manos-space/TAS_kc/keycaps/SLS/sldprt/r0/r0_c3.SLDPRT

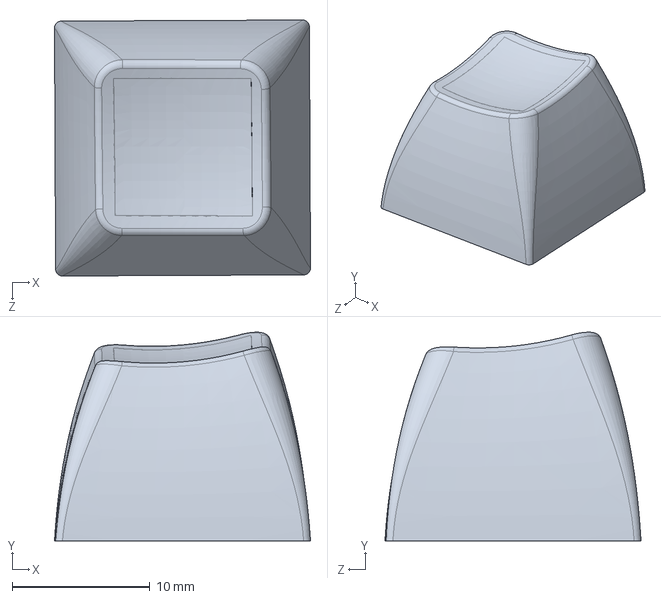
[picture p15: CAD file, 2020-01-13]
keycaps/SLS/sldprt/r0/r0_c3.SLDPRT
18.6 x 15.1 x 18.6 mm
