manos-space/TAS_kc/keycaps/SLS/sldprt/r1/r1_c1.SLDPRT

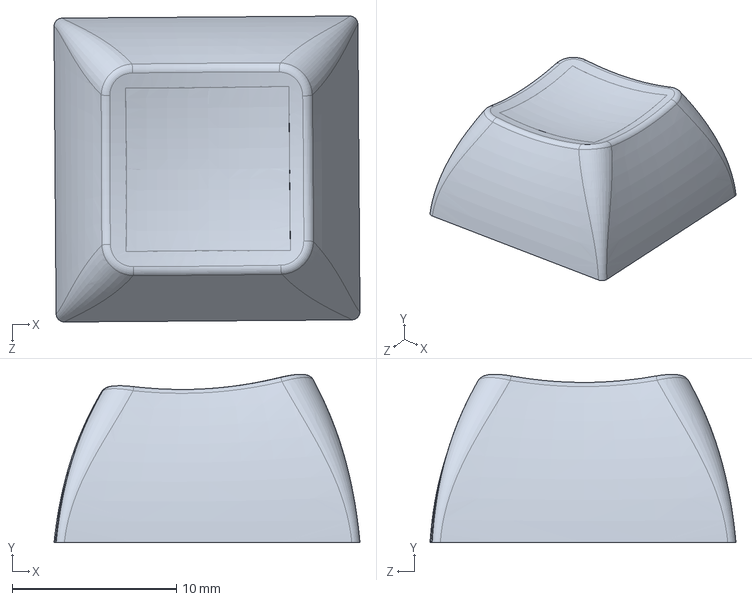
[picture p16: CAD file, 2020-01-13]
keycaps/SLS/sldprt/r1/r1_c1.SLDPRT
18.6 x 10.3 x 18.6 mm
