manos-space/TAS_kc/keycaps/SLS/sldprt/r3/r3-1.25u.SLDPRT

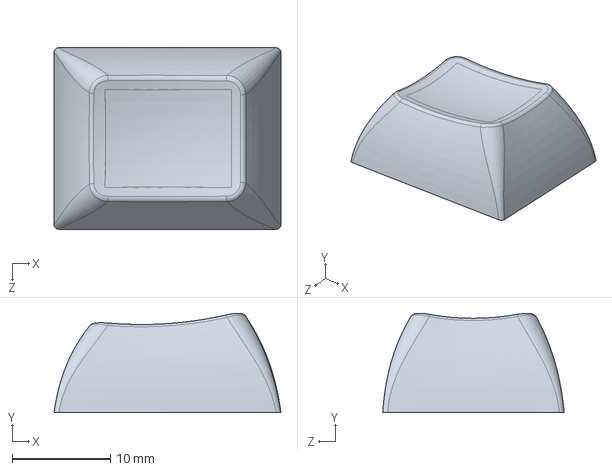
[picture p17: CAD file, 2020-01-13]
keycaps/SLS/sldprt/r3/r3-1.25u.SLDPRT
23.1 x 10.1 x 18.5 mm
