manos-space/TAS_kc/keycaps/SLS/sldprt/rn/rn_c1_mirrored.SLDPRT

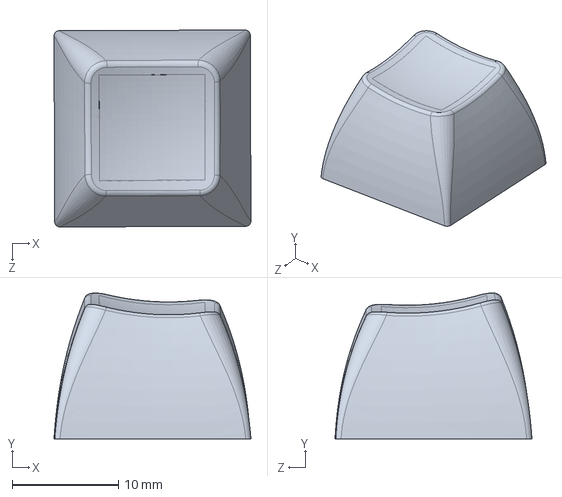
[picture p18: CAD file, 2020-01-07]
keycaps/SLS/sldprt/rn/rn_c1_mirrored.SLDPRT
18.6 x 13.8 x 18.6 mm
