manos-space/TAS_kc/keycaps/SLS/sldprt/r2/r2_c2.SLDPRT

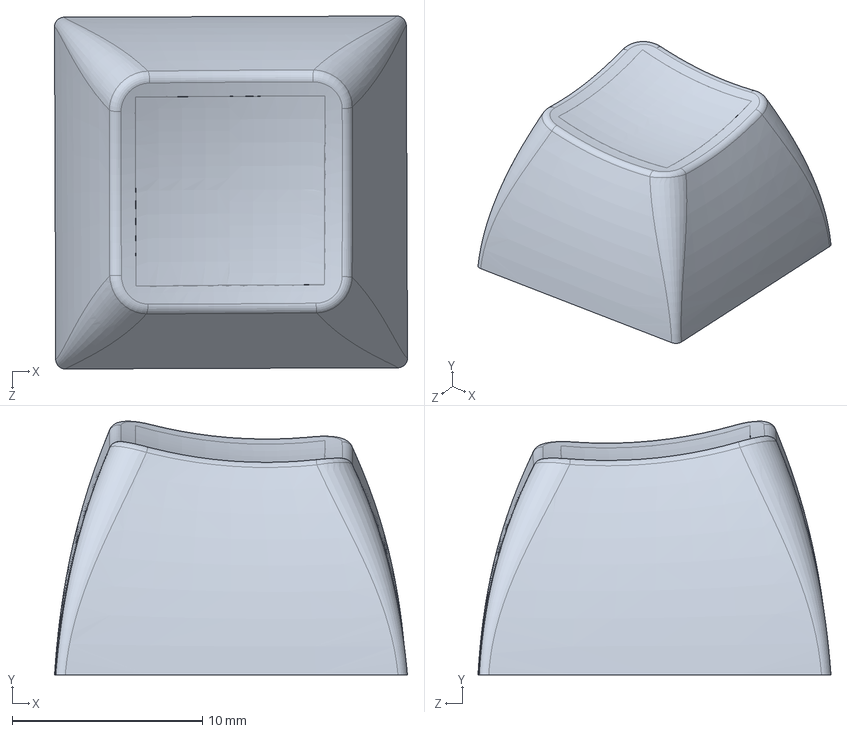
[picture p19: CAD file, 2020-01-13]
keycaps/SLS/sldprt/r2/r2_c2.SLDPRT
18.6 x 13.3 x 18.6 mm
