manos-space/TAS_kc/keycaps/SLS/sldprt/rn/rn_c2_mirrored.SLDPRT

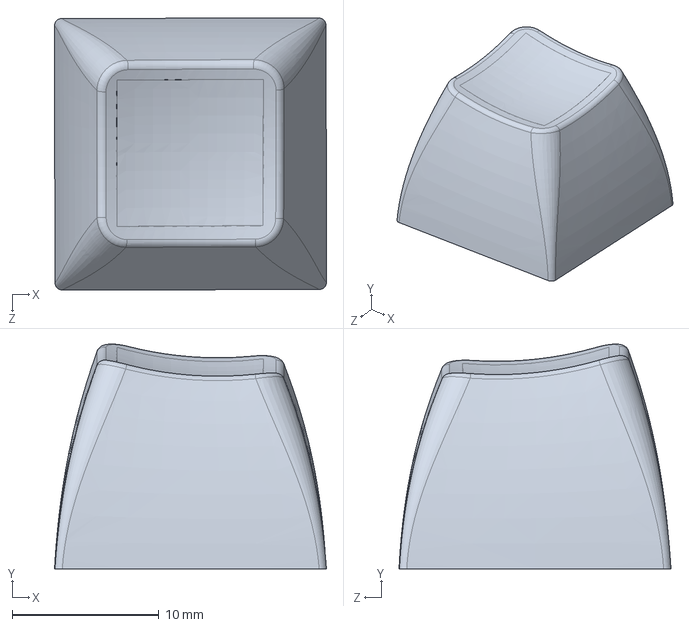
[picture p20: CAD file, 2020-01-07]
keycaps/SLS/sldprt/rn/rn_c2_mirrored.SLDPRT
18.5 x 15.3 x 18.5 mm
