manos-space/TAS_kc/keycaps/SLS/sldprt/rn/rn_c0.SLDPRT

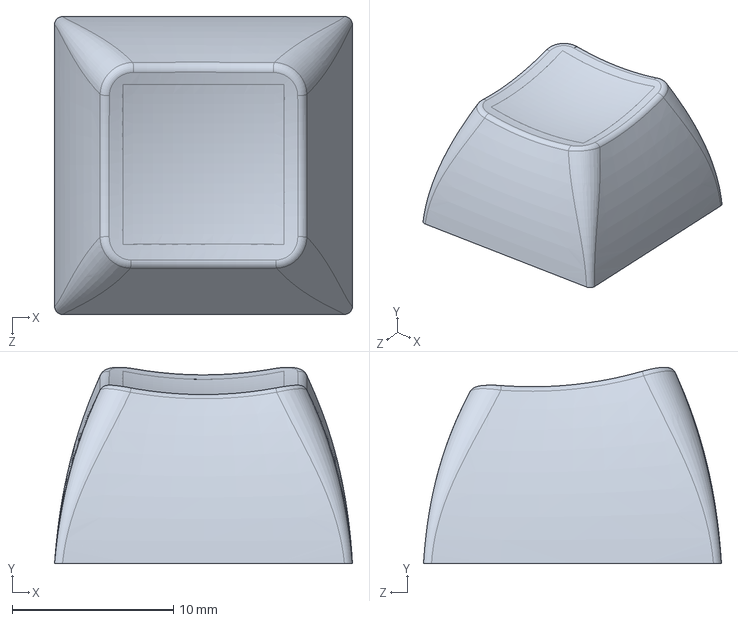
[picture p21: CAD file, 2020-01-07]
keycaps/SLS/sldprt/rn/rn_c0.SLDPRT
18.5 x 12.2 x 18.5 mm
